meerstern/DigitalVideoShield/img1.jpg

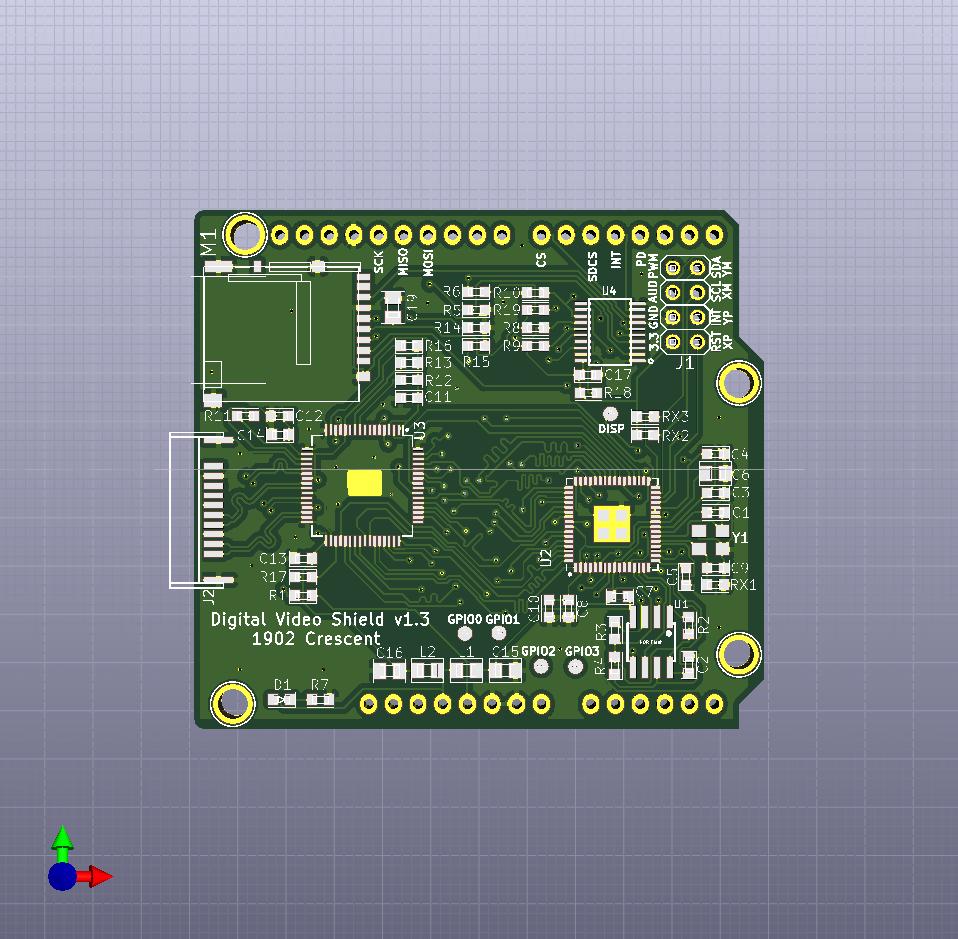
img1.jpg
