meerstern/DigitalVideoShield/img2.jpg

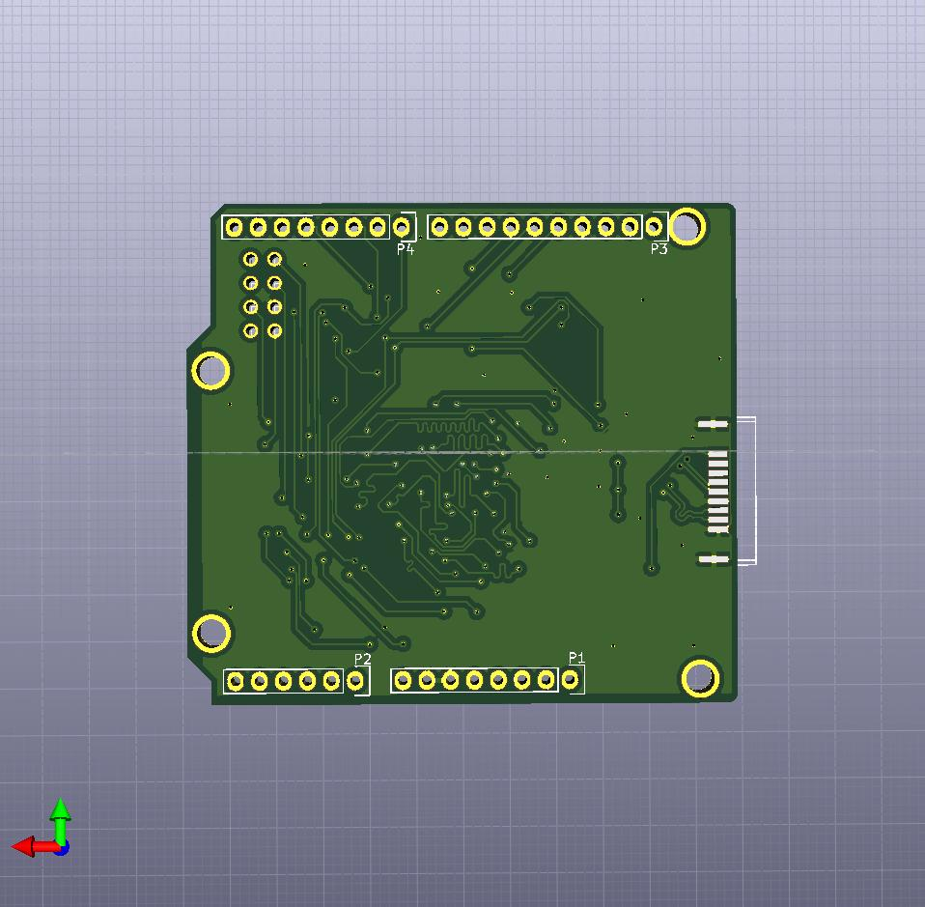
img2.jpg
