meerstern/DigitalVideoShield/SampleCode/STM32F401_Nucleo/STM32F401_BT81X/Src/main.c

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

/* Includes ------------------------------------------------------------------*/
#include "main.h"
#include "fatfs.h"
#include "spi.h"
#include "usart.h"
#include "gpio.h"

/* USER CODE BEGIN Includes */
#include "BT8XX.h"
#include "fatfs.h"
/* USER CODE END Includes */


void SystemClock_Config(void);
/* USER CODE BEGIN 0 */
int _write( int file, char *ptr, int len )
{
  HAL_UART_Transmit(&huart2,(uint8_t*) ptr, len, 1000);
  return len;
}
/* USER CODE END 0 */

/**
  * @brief  The application entry point.
  * @retval int
  */
int main(void)
{
  

  /* MCU Configuration--------------------------------------------------------*/

  /* Reset of all peripherals, Initializes the Flash interface and the Systick. */
  HAL_Init();

  /* Configure the system clock */
  SystemClock_Config();

  /* Initialize all configured peripherals */
  MX_GPIO_Init();
  MX_USART2_UART_Init();
  MX_SPI1_Init();
  MX_FATFS_Init();
  /* USER CODE BEGIN 2 */

  printf("Initialize Success!!\r\n");
  EveInit();

#ifdef ENABLE_SD
  if(f_mount(&fs, "", 0) != FR_OK)
	  printf("SD Mount ERR\n\r");
  HAL_Delay(10);
  if(f_open(&fp, "test.txt", FA_OPEN_ALWAYS | FA_READ | FA_WRITE) != FR_OK)
	  printf("SD Write ERR\n\r");
  HAL_Delay(10);
  f_puts("SD Card Test\n", &fp);
  HAL_Delay(10);
  if(f_close(&fp) != FR_OK)
	  printf("SD File Close ERR\n\r");
  HAL_Delay(10);
  if(f_mount(NULL, "", 1) != FR_OK)
	  printf("SD Unmount ERR\n\r");
#endif

  /* USER CODE END 2 */

  /* Infinite loop */
  /* USER CODE BEGIN WHILE */
  while (1)
  {
    /* USER CODE END WHILE */

    /* USER CODE BEGIN 3 */


	  uint16_t cnt;
	  cnt=0;


	  while(CHIP_ID_RESET!=EveReadChipID()){
		  cnt++;
		  if(cnt>100){
			  printf("EVE NOT Found!! :0x%x  \r\n",EveReadChipID());
			  HAL_Delay(100);
			  break;
		  }
	  }
	  if(cnt<100)printf("EVE Found!!\r\n");



	  cnt=0;
	  while(0x0!=EveCheckStatus()){
		  cnt++;
		  if(cnt>100){
			  printf("EVE NOT Active!! :%d  \r\n",EveCheckStatus());
			  HAL_Delay(200);
		  }
	  }
	  if(cnt<100)printf("EVE Active!!\r\n");


	  EveSetCPUFrq();

	  EveSetResolution();
	  //EveCheckFlashState();
	  //EveFlashTest();

	  EveDemo();
//	  EveDemo2();
//	  EveDemo3();
	  while(1){

	  }




  }
  /* USER CODE END 3 */
}

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
